tebl/C64-BlinkenDiag/gallery/2021-03-16 19.02.30.jpg

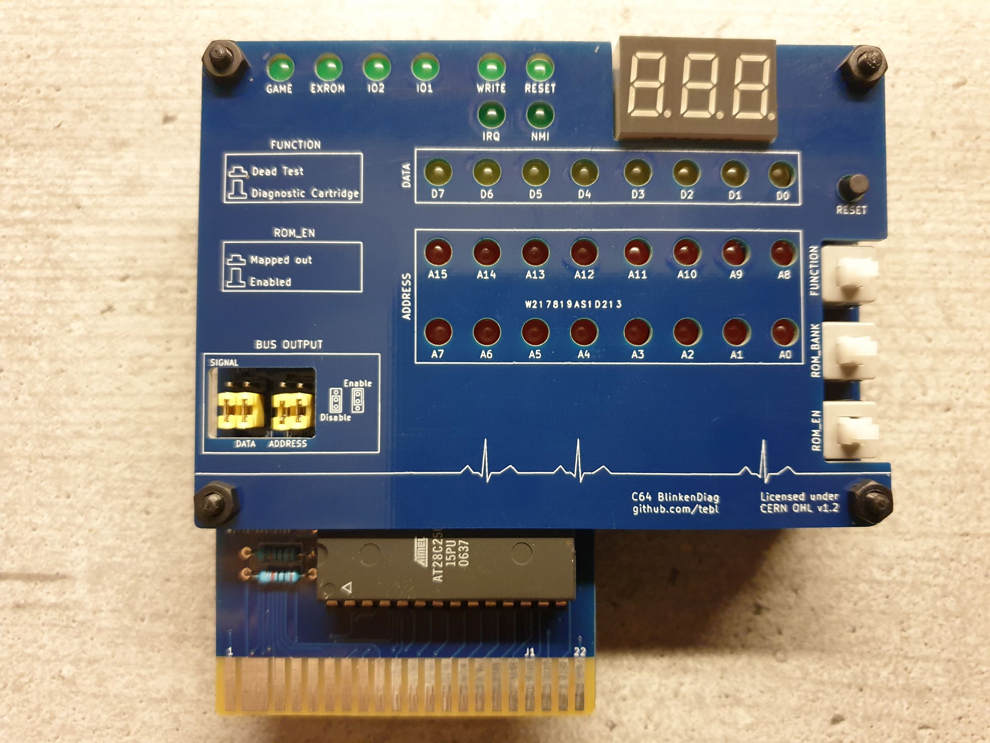
gallery/2021-03-16 19.02.30.jpg
