tebl/C64-BlinkenDiag/gallery/C64 BlinkenDiag Faceplate.png

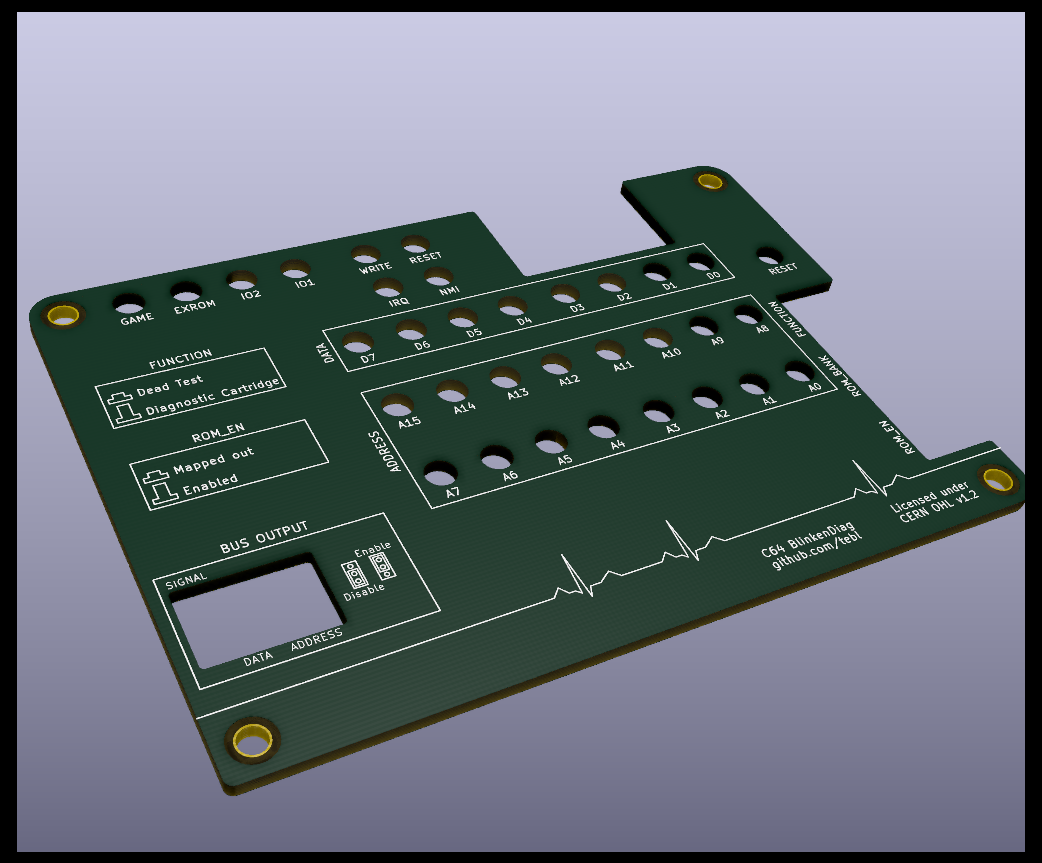
gallery/C64 BlinkenDiag Faceplate.png
